Jeffrey-McCormick/CPTR480-ENGR357_Quadrature_SDR/Pictures/HighpassFilterSimulations.png

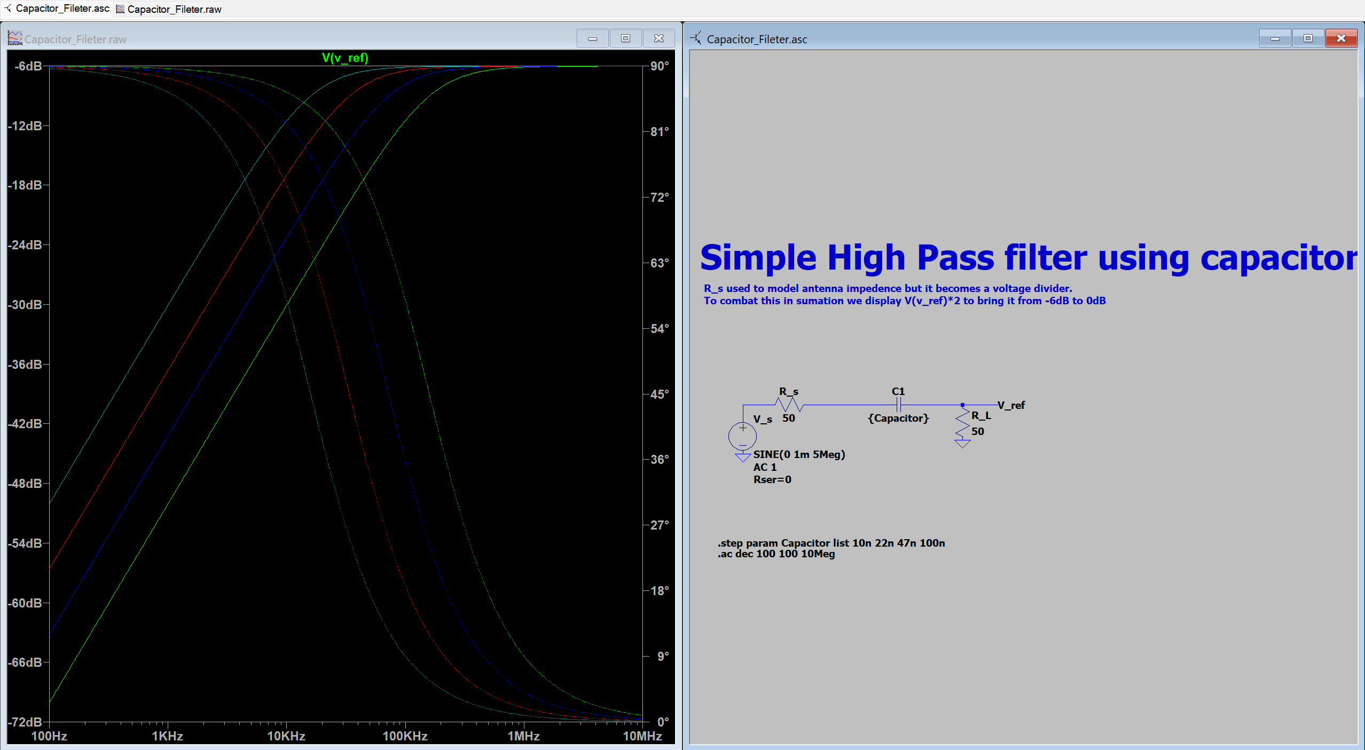
Pictures/HighpassFilterSimulations.png
