Jeffrey-McCormick/CPTR480-ENGR357_Quadrature_SDR/Pictures/Transformer_Turns_Calc.png

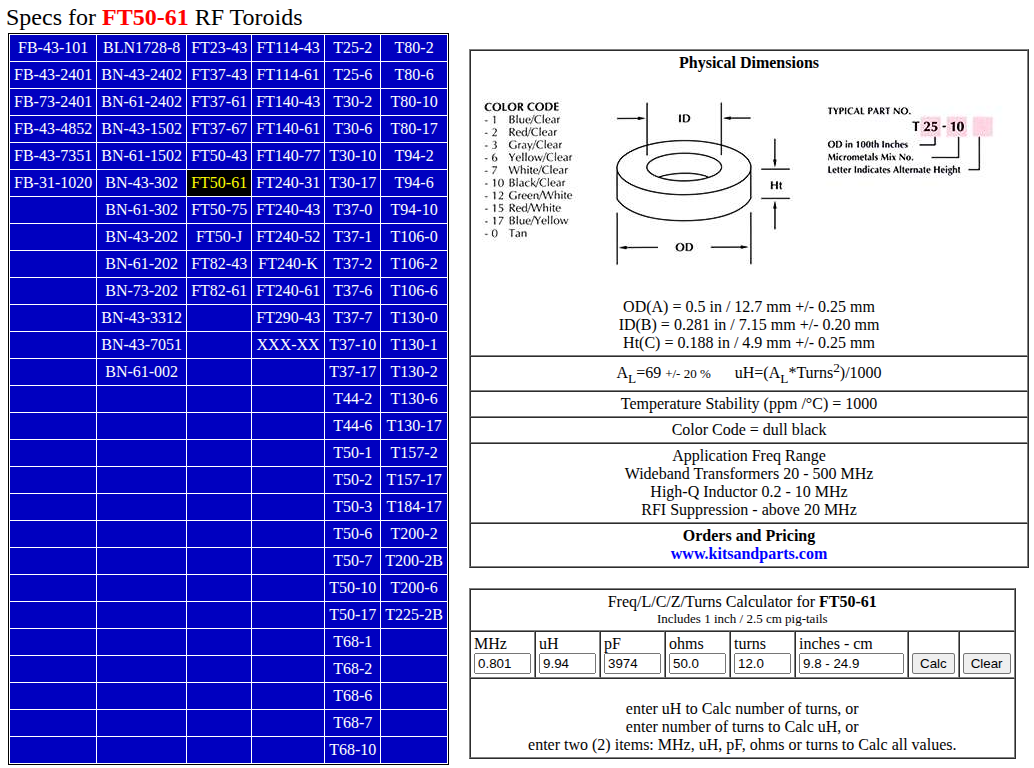
Pictures/Transformer_Turns_Calc.png
