Jeffrey-McCormick/CPTR480-ENGR357_Quadrature_SDR/LTSpice_Simulations/Antenna_BP_Filter.asc

C1: cap; {C_top}
C2: cap; {C_down_L}
C3: cap; {C_top}
C4: cap; {C_down_R}
C5: cap; {C_down_R}
L1: ind; {L_top}
L2: ind; {L_down}
L3: ind; {L_top}
R1: res; 50
Vp: voltage; SINE(0 1m 5Meg); AC 1 0; Rser=0
Named nets: 0, V_RF
.ac dec 100 1Meg 50Meg
.noise V(V_RF) Vp dec 100 1k 100Meg
.param C_top=330pF C_down_L=330p L_down=442n L_top=663n C_down_R=100pF
Bandpass Filter for HF Band
param C_top=353pF L_top=663n C_down=530p L_down=442n
