Jeffrey-McCormick/CPTR480-ENGR357_Quadrature_SDR/LTSpice_Simulations/LP_filter.asc

C1: cap; 100n
C2: cap; 2.2n
C3: cap; 2.2n
C4: cap; 2.2n
C5: cap; 330p
C6: cap; 100p
C7: cap; 2.2n
C8: cap; 330p
C9: cap; 100p
L1: ind; 7.95µ
V2: voltage; ""; AC 1; Rser=50
Named nets: 0, I_Input, I_SIGNAL
.ac dec 100 100 10Meg
Low Pass Filter
Antenna Low Pass Filter for AM Frequencies
<2MHz
