Jeffrey-McCormick/CPTR480-ENGR357_Quadrature_SDR/LTSpice_Simulations/VrefAmplifierSimulations.asc

C1: cap; 10µ
R1: res; 1000
R2: res; 10
U1: OP213
V1: voltage; 4.7
V2: voltage; SINE(2.35 0.1 50k)
V3: voltage
Named nets: 0, VDDA, Vref/2
.tran 0 2m 0 1u
