Jeffrey-McCormick/CPTR480-ENGR357_Quadrature_SDR/LTSpice_Simulations/Capacitor_Fileter.asc

C1: cap; {Capacitor}
R_L: res; 50
R_s: res; 50
V_s: voltage; SINE(0 1m 5Meg); AC 1; Rser=0
Named nets: 0, V_ref
.step param Capacitor list 10n 22n 47n 100n
.ac dec 100 100 10Meg
R_s used to model antenna impedence but it becomes a voltage divider.
To combat this in sumation we display V(v_ref)*2 to bring it from -6dB to 0dB
Simple High Pass filter using capacitor
