Jeffrey-McCormick/CPTR480-ENGR357_Quadrature_SDR/Software/test_playback.py

# The MIT License (MIT)
# Copyright (c) 2022 Mike Teachman
# https://opensource.org/licenses/MIT

# Purpose:  Play a pure audio tone out of a speaker or headphones
#
# - write audio samples containing a pure tone to an I2S amplifier or DAC module
# - tone will play continuously in a loop until
#   a keyboard interrupt is detected or the board is reset
#
# Blocking version
# - the write() method blocks until the entire sample buffer is written to I2S

import os
import math
import struct
from machine import I2S
from machine import Pin
from machine import PWM

def make_tone(rate, bits, frequency):
    # create a buffer containing the pure tone samples
    samples_per_cycle = rate // frequency
    sample_size_in_bytes = bits // 8
    samples = bytearray(samples_per_cycle * sample_size_in_bytes)
    volume_reduction_factor = 32
    range = pow(2, bits) // 2 // volume_reduction_factor
    
    if bits == 16:
        format = "<h"
    else:  # assume 32 bits
        format = "<l"
    
    for i in range(samples_per_cycle):
        sample = range + int((range - 1) * math.sin(2 * math.pi * i / samples_per_cycle))
        struct.pack_into(format, samples, i * sample_size_in_bytes, sample)
        
    return samples

if os.uname().machine.count("PYBv1"):

    # ======= I2S CONFIGURATION =======
    SCK_PIN = "Y6"
    WS_PIN = "Y5"
    SD_PIN = "Y8"
    I2S_ID = 2
    BUFFER_LENGTH_IN_BYTES = 2000
    # ======= I2S CONFIGURATION =======

elif os.uname().machine.count("PYBD"):
    import pyb

    pyb.Pin("EN_3V3").on()  # provide 3.3V on 3V3 output pin

    # ======= I2S CONFIGURATION =======
    SCK_PIN = "Y6"
    WS_PIN = "Y5"
    SD_PIN = "Y8"
    I2S_ID = 2
    BUFFER_LENGTH_IN_BYTES = 2000
    # ======= I2S CONFIGURATION =======

elif os.uname().machine.count("ESP32"):

    # ======= I2S CONFIGURATION =======
    SCK_PIN = 32
    WS_PIN = 25
    SD_PIN = 33
    I2S_ID = 0
    BUFFER_LENGTH_IN_BYTES = 2000
    # ======= I2S CONFIGURATION =======

elif os.uname().machine.count("Raspberry"):

    # ======= I2S CONFIGURATION =======
    SCK_PIN = 15
    WS_PIN = 16
    SD_PIN = 14
    I2S_ID = 0
    MCLK = 17
    BUFFER_LENGTH_IN_BYTES = 2000
    # ======= I2S CONFIGURATION =======

elif os.uname().machine.count("MIMXRT"):

    # ======= I2S CONFIGURATION =======
    SCK_PIN = 4
    WS_PIN = 3
    SD_PIN = 2
    I2S_ID = 2
    BUFFER_LENGTH_IN_BYTES = 2000
    # ======= I2S CONFIGURATION =======

else:
    print("Warning: program not tested with this board")

# ======= AUDIO CONFIGURATION =======
TONE_FREQUENCY_IN_HZ = 440
SAMPLE_SIZE_IN_BITS = 32
FORMAT = I2S.MONO  # only MONO supported in this example
SAMPLE_RATE_IN_HZ = 22_050
# ======= AUDIO CONFIGURATION =======

mclk = PWM(Pin(MCLK))
mclk.freq(SAMPLE_RATE_IN_HZ * 256)
mclk.duty_u16(32768)

Pin(6, Pin.OUT).value(1)

audio_out = I2S(
    I2S_ID,
    sck=Pin(SCK_PIN),
    ws=Pin(WS_PIN),
    sd=Pin(SD_PIN),
    mode=I2S.TX,
    bits=SAMPLE_SIZE_IN_BITS,
    format=FORMAT,
    rate=SAMPLE_RATE_IN_HZ,
    ibuf=BUFFER_LENGTH_IN_BYTES,
)

samples = make_tone(SAMPLE_RATE_IN_HZ, SAMPLE_SIZE_IN_BITS, TONE_FREQUENCY_IN_HZ)

# continuously write tone sample buffer to an I2S DAC
print("==========  START PLAYBACK ==========")
try:
    while True:
        num_written = audio_out.write(samples)

except (KeyboardInterrupt, Exception) as e:
    print("caught exception {} {}".format(type(e).__name__, e))

# cleanup
audio_out.deinit()
print("Done")
